croningp/InorganicClusterDiscovery/clusterbot/hardware/Prints/Stirring ring/Magnet housing 2.2kg pull rectangular.stl

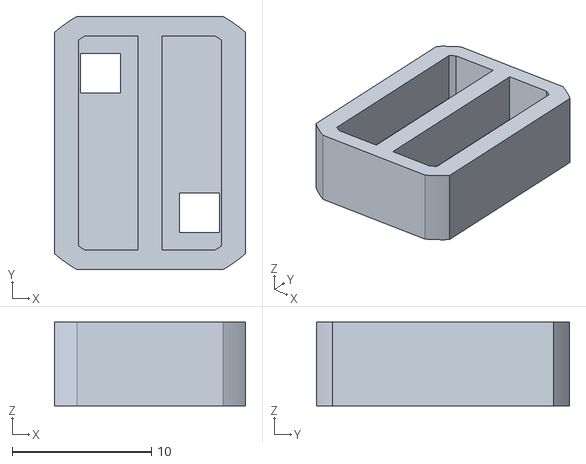
[picture p18: CAD file, 2020-04-06]
clusterbot/hardware/Prints/Stirring ring/Magnet housing 2.2kg pull rectangular.stl
13.7 x 18.2 x 6.00
