croningp/InorganicClusterDiscovery/clusterbot/hardware/Prints/Stirring ring/PCB mounting block.stl

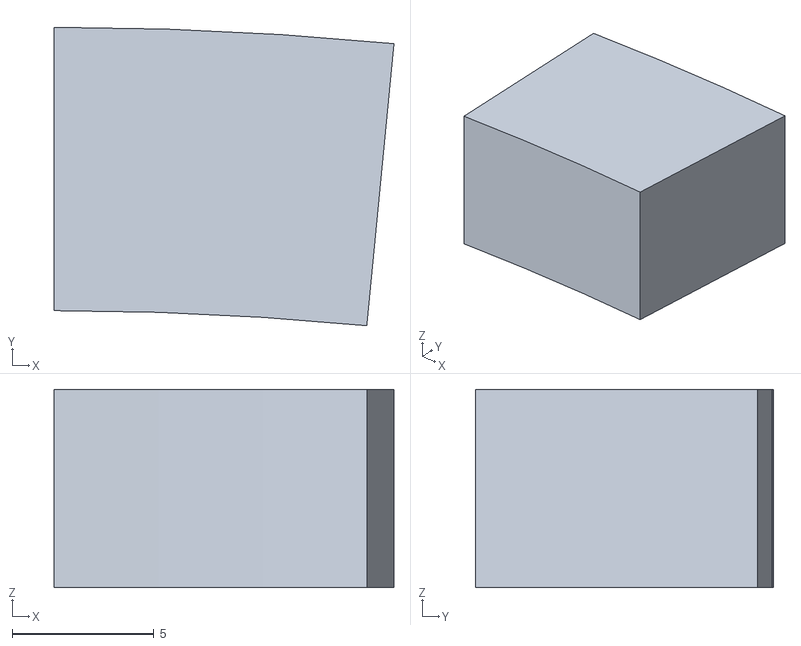
[picture p19: CAD file, 2020-04-06]
clusterbot/hardware/Prints/Stirring ring/PCB mounting block.stl
12.0 x 10.5 x 7.00
