croningp/InorganicClusterDiscovery/clusterbot/hardware/StirringRingPCB/parts/ring.sldprt

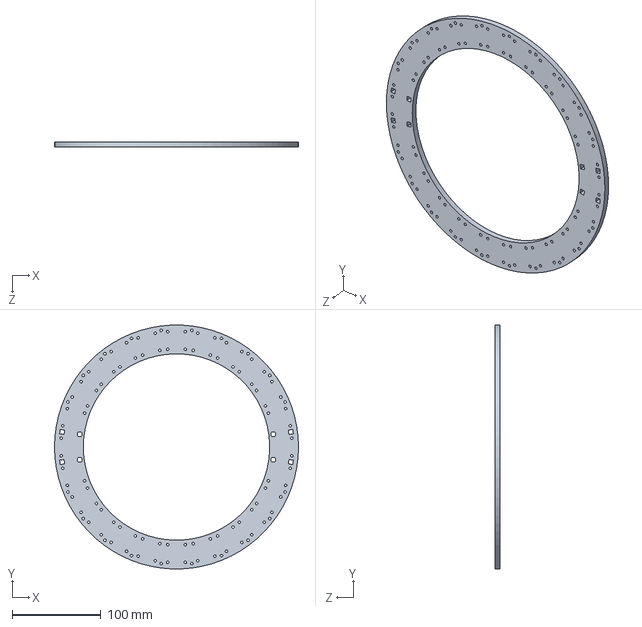
[picture p20: CAD file, 2020-04-06]
clusterbot/hardware/StirringRingPCB/parts/ring.sldprt
275.0 x 274.8 x 6.00 mm
