croningp/InorganicClusterDiscovery/clusterbot/hardware/StirringRingPCB/parts/plate.sldprt

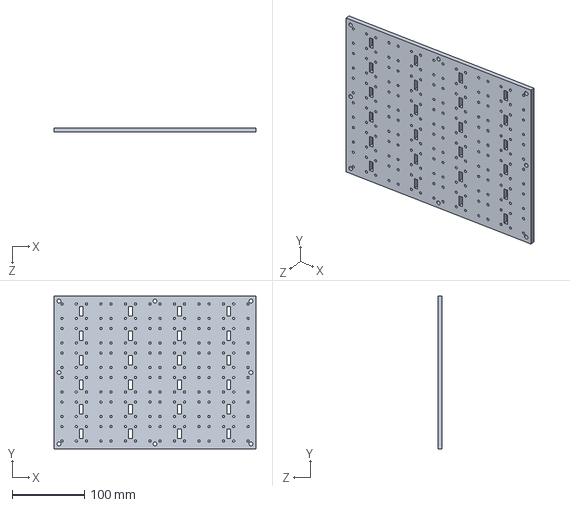
[picture p21: CAD file, 2020-04-06]
clusterbot/hardware/StirringRingPCB/parts/plate.sldprt
280.0 x 212.0 x 6.00 mm
