croningp/InorganicClusterDiscovery/clusterbot/hardware/StirringRingPCB/parts/XHP-2.STEP

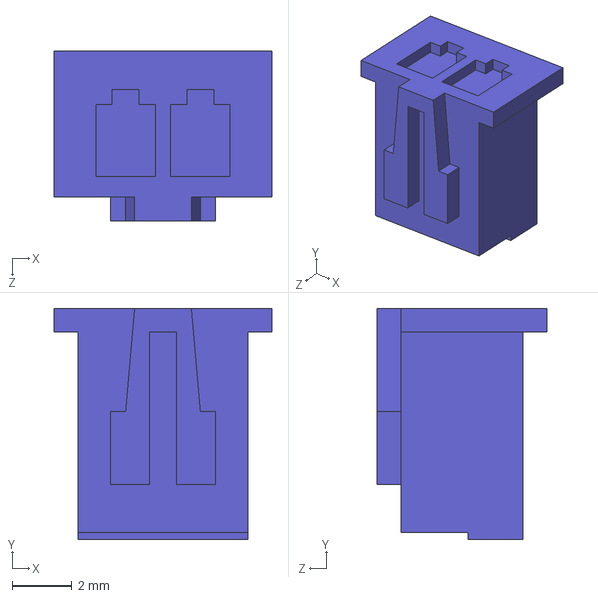
[picture p22: CAD file, 2020-04-06]
clusterbot/hardware/StirringRingPCB/parts/XHP-2.STEP
7.30 x 7.75 x 5.70 mm
